GregGoldman/BlinkLight/Electrical/FINAL OUTPUTS/PCB Photo1.jpg

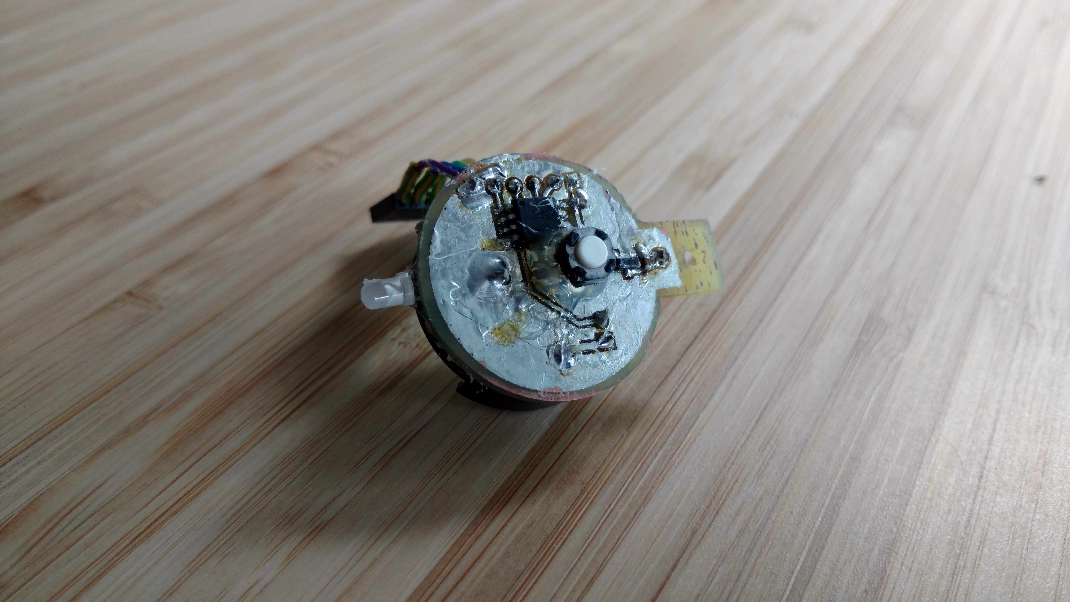
Electrical/FINAL OUTPUTS/PCB Photo1.jpg
