GregGoldman/BlinkLight/Electrical/FINAL OUTPUTS/PCB Photo 3.jpg

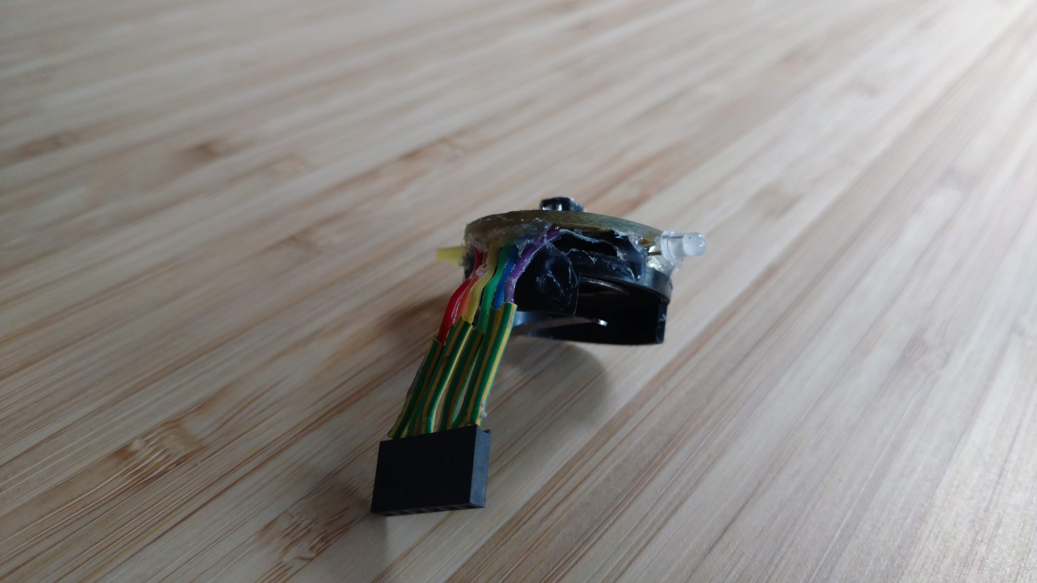
Electrical/FINAL OUTPUTS/PCB Photo 3.jpg
