GregGoldman/BlinkLight/Electrical/Milestone 4/Outputs/3d.PNG

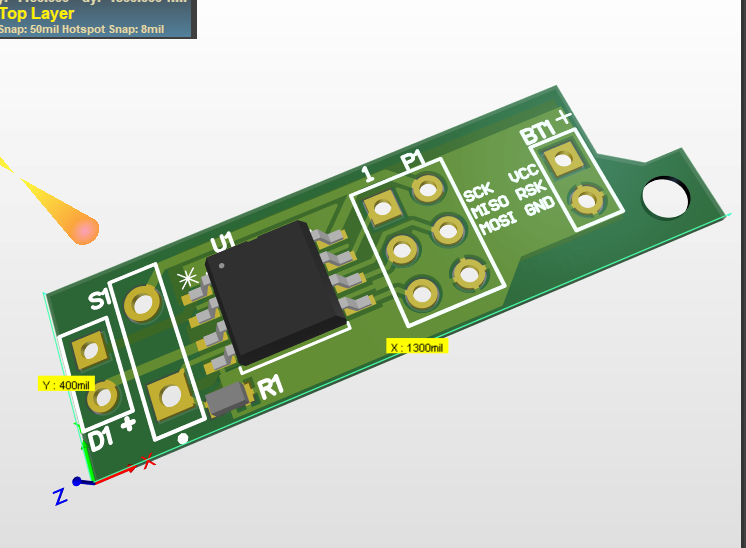
Electrical/Milestone 4/Outputs/3d.PNG
