GregGoldman/BlinkLight/Electrical/Milestone 4/Outputs/layout bottom.PNG

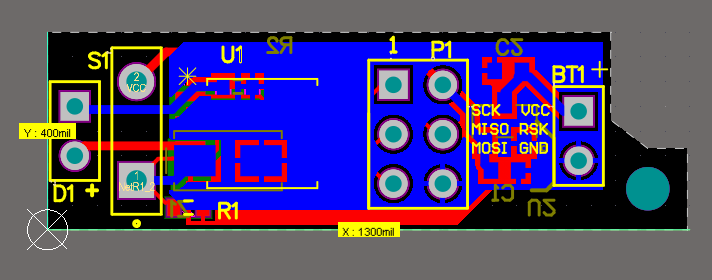
Electrical/Milestone 4/Outputs/layout bottom.PNG
