GregGoldman/BlinkLight/Electrical/Milestone 4/Outputs/layout top.PNG

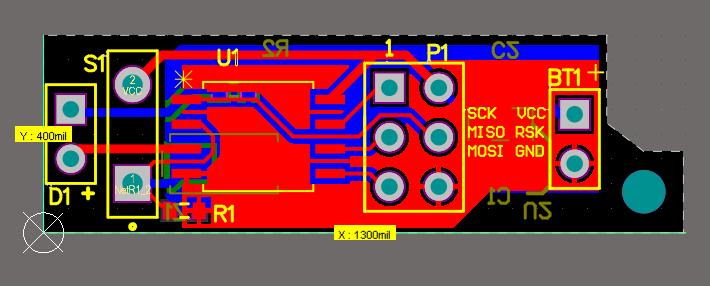
Electrical/Milestone 4/Outputs/layout top.PNG
