GregGoldman/BlinkLight/Electrical/Altium Designer/Parts/sot23-package-1.snapshot.6/SOT23-6.stp

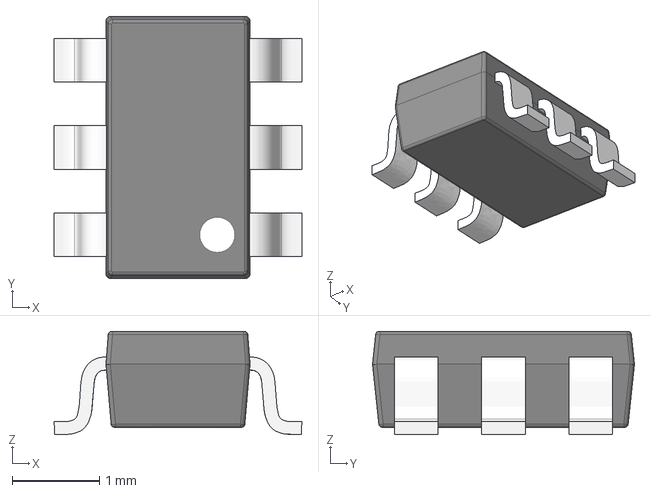
[picture p23: CAD file, 2018-11-10]
Electrical/Altium Designer/Parts/sot23-package-1.snapshot.6/SOT23-6.stp
2.84 x 3.00 x 1.18 mm
