GregGoldman/BlinkLight/Mechanical/Final Design/Base.sldprt

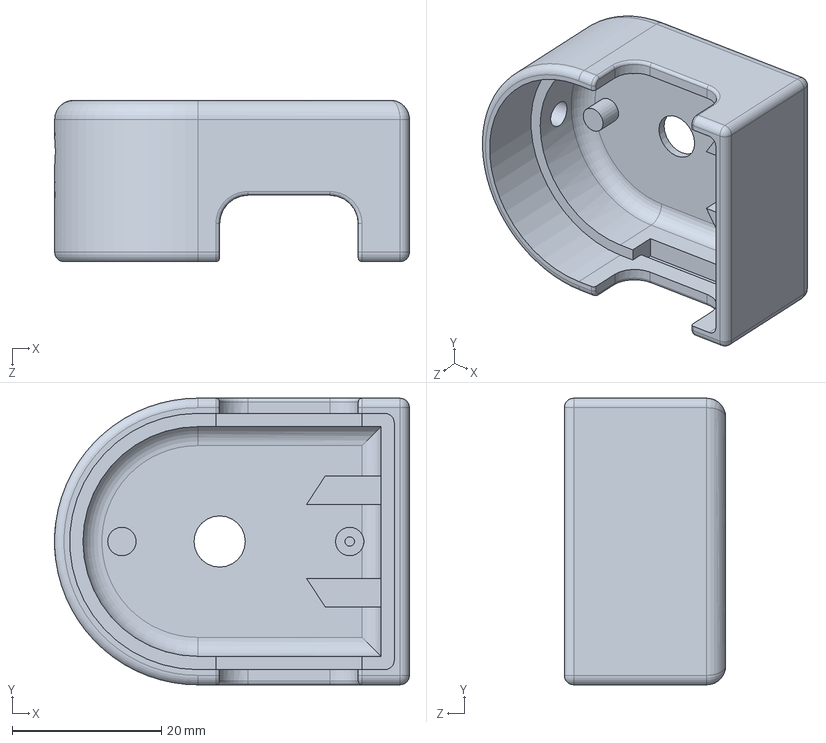
[picture p24: CAD file, 2018-12-05]
Mechanical/Final Design/Base.sldprt
47.5 x 38.4 x 21.6 mm
