GregGoldman/BlinkLight/Mechanical/Millenium falcon design/HousingTop.SLDPRT

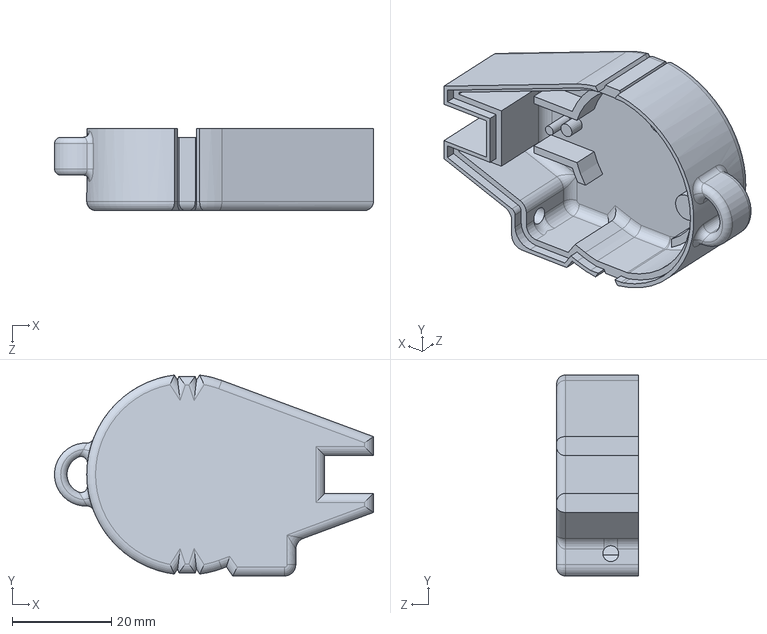
[picture p25: CAD file, 2018-11-19]
Mechanical/Millenium falcon design/HousingTop.SLDPRT
64.1 x 40.4 x 16.5 mm
