GregGoldman/BlinkLight/Mechanical/Final Design/TopSTL.STL

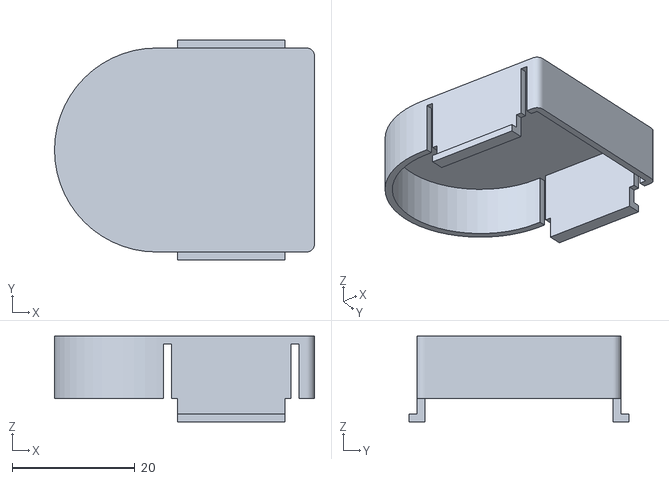
[picture p27: CAD file, 2018-12-05]
Mechanical/Final Design/TopSTL.STL
42.4 x 35.8 x 14.0
