GregGoldman/BlinkLight/Mechanical/Body1.STL

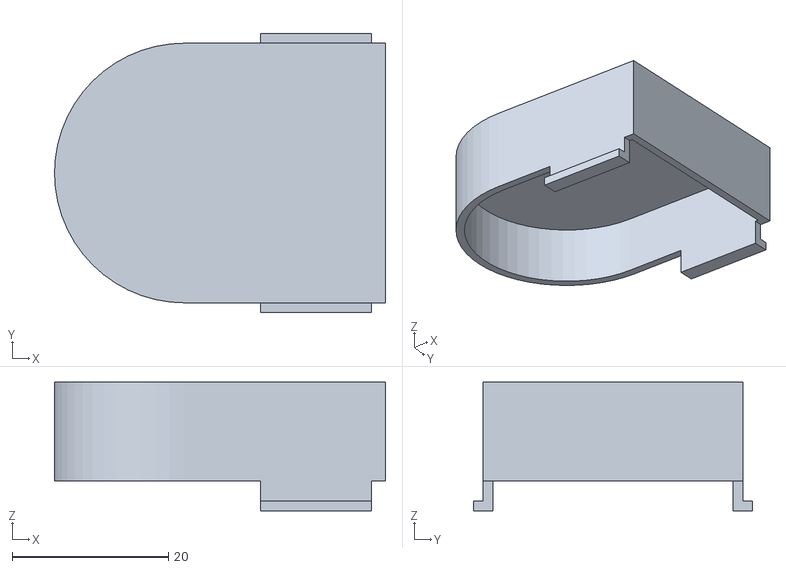
[picture p28: CAD file, 2018-12-05]
Mechanical/Body1.STL
42.4 x 35.8 x 16.5
