GregGoldman/BlinkLight/Mechanical/Body2.STL

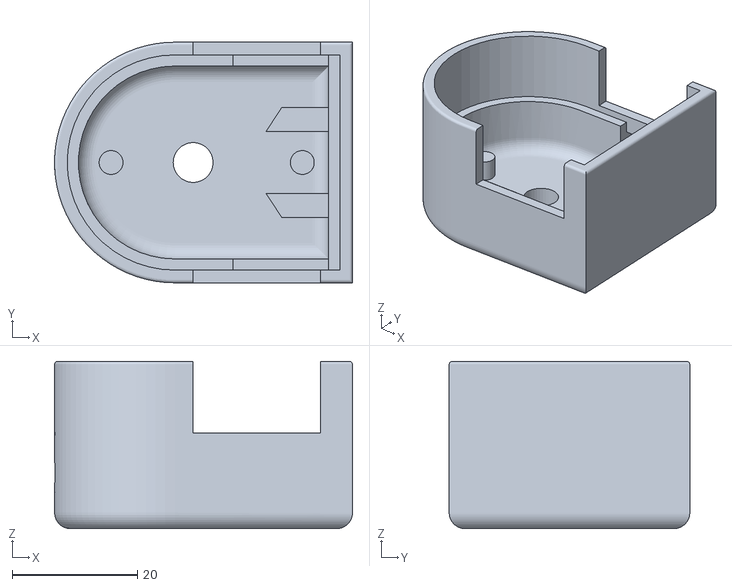
[picture p29: CAD file, 2018-12-05]
Mechanical/Body2.STL
47.5 x 38.4 x 26.7
