GregGoldman/BlinkLight/Mechanical/split_test.sldprt

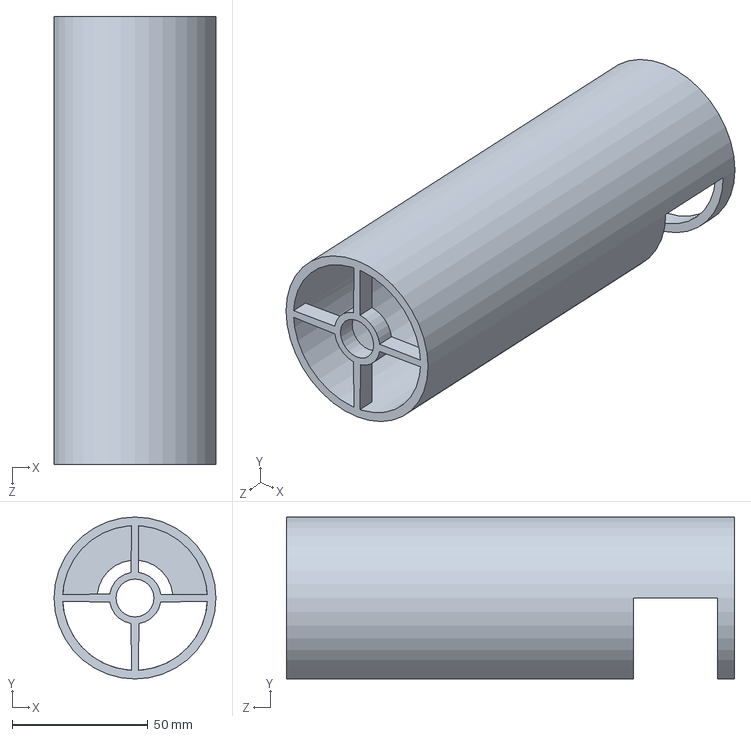
[picture p30: CAD file, 2018-12-05]
Mechanical/split_test.sldprt
59.7 x 59.7 x 165.1 mm
