GregGoldman/BlinkLight/Mechanical/meh.DXF

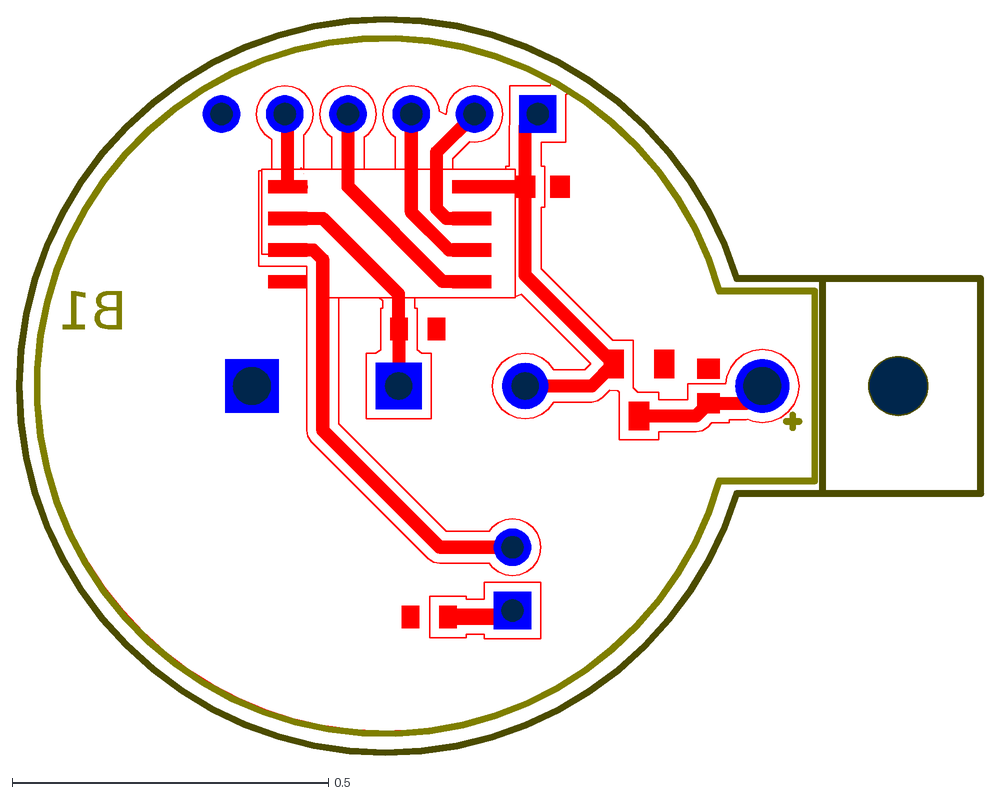
[picture p31: CAD file, 2018-12-05]
Mechanical/meh.DXF
B1
