GregGoldman/BlinkLight/Mechanical/BlinkLight_NewBat.step

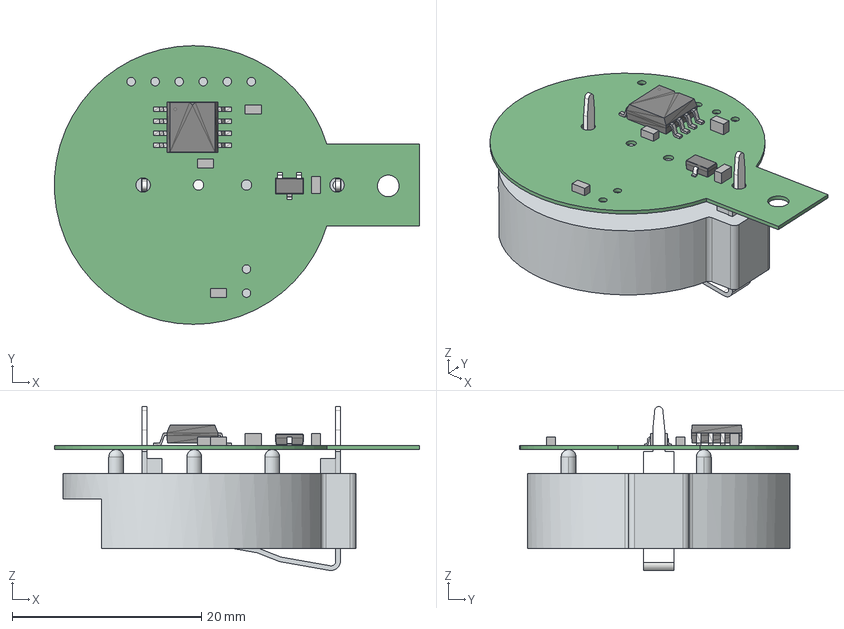
[picture p32: CAD file, 2018-11-19]
Mechanical/BlinkLight_NewBat.step
38.6 x 29.5 x 17.3 mm
Board
keystone-PN1025-7
SOT23-3
Extruded x 5
8S2
