GregGoldman/BlinkLight/Mechanical/Final Design/Photos/Assembly1.PNG

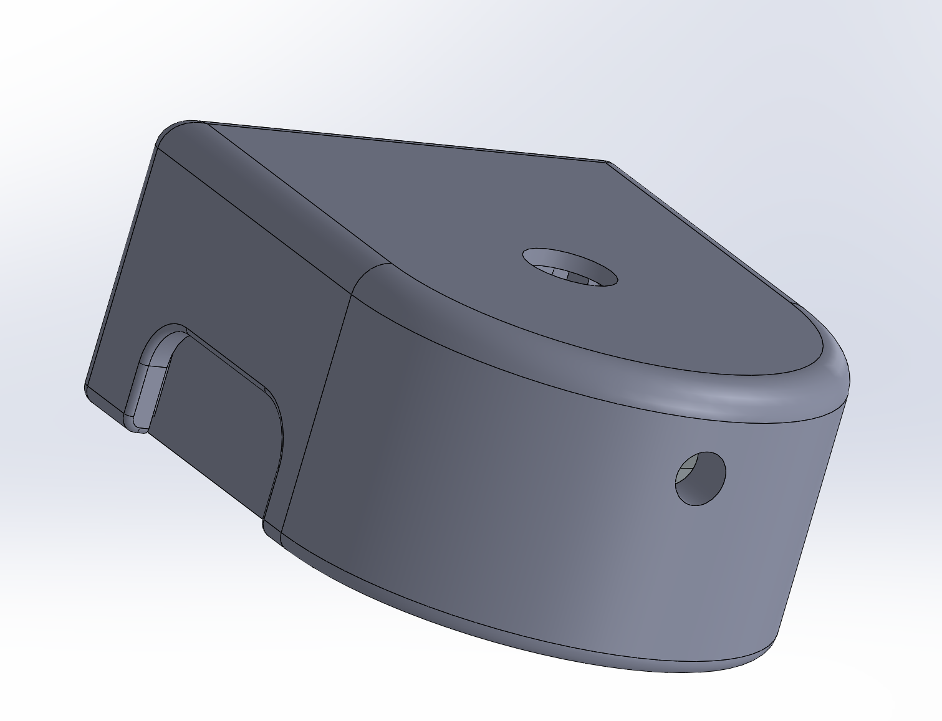
Mechanical/Final Design/Photos/Assembly1.PNG
