GregGoldman/BlinkLight/Mechanical/Final Design/Photos/Assembly2.PNG

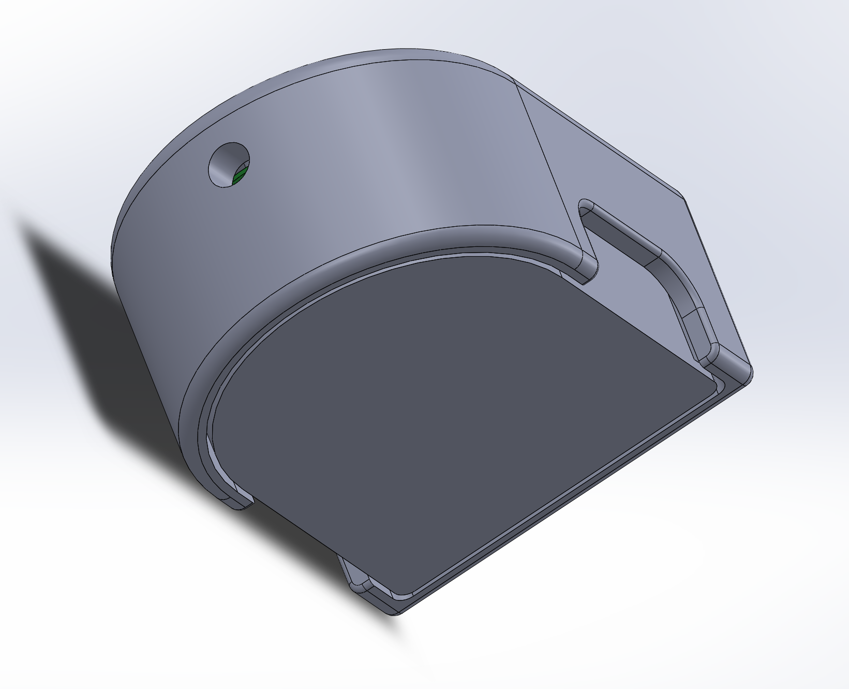
Mechanical/Final Design/Photos/Assembly2.PNG
