GregGoldman/BlinkLight/Mechanical/Final Design/Photos/Assembly_Cross_Section2.PNG

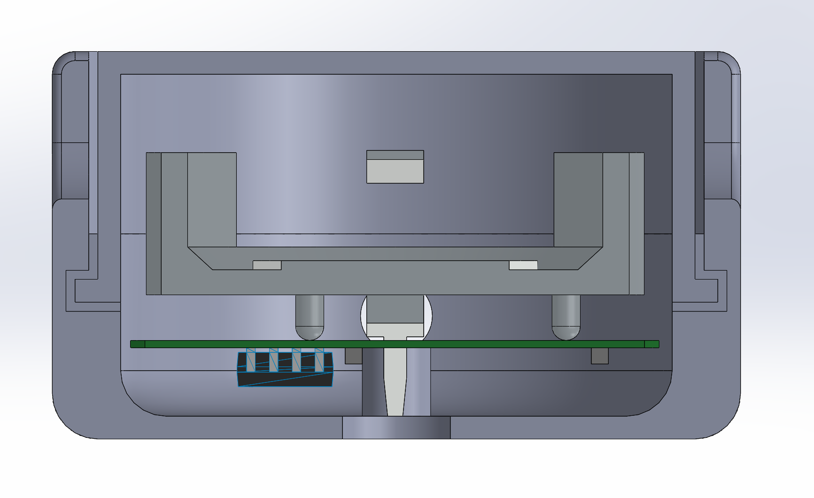
Mechanical/Final Design/Photos/Assembly_Cross_Section2.PNG
