GregGoldman/BlinkLight/Electrical/Rough circuit drafts.pdf

# Circuit Diagram

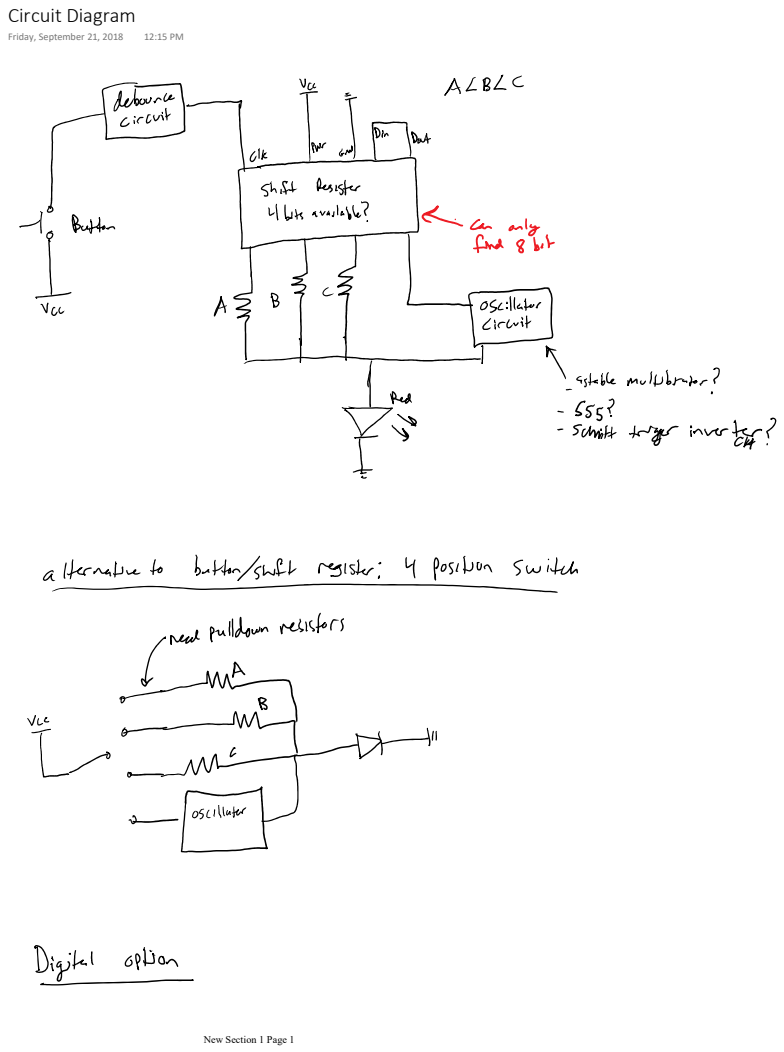
[picture p38: page 1]
Friday, September 21, 2018

New Section 1 Page 1

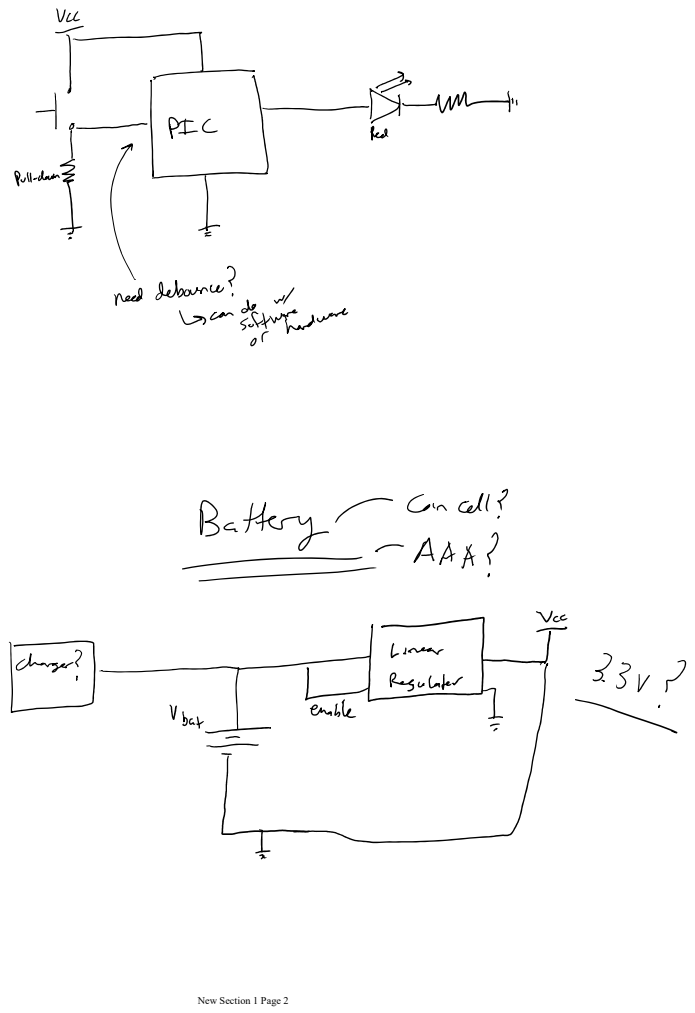
[picture p39: page 2]

New Section 1 Page 2
